Safonovdv91/MG-Lap-Race-Timer/src/modules/web_handlers.cpp

/** 
 * Обработчики веб-запросов.
 */
#include <ArduinoJson.h>
#include <FS.h>
#include <SPIFFS.h>

#include "modules/web_handlers.h"
#include "utils/config.h"
#include "core/measurement_core.h"
#include "modules/web_content.h"
#include "drivers/battery/battery.h"

#ifdef RECEIVER_MODE
#include "modules/transmitter_data.h"  // ← теперь всё живёт здесь
#endif

WebServer server(80);

// Внешние переменные (определены в других файлах)
extern Mode currentMode;

// Переменные для хранения данных излучателя (только для режима приемника)
#ifdef RECEIVER_MODE

#endif

// ============================================================================
// * Все данные обновляются через WebSocket (JavaScript)
// ============================================================================

void sendHtmlFile(const char* path) {
  if (SPIFFS.exists(path)) {
    File file = SPIFFS.open(path, "r");
    if (file) {
      server.streamFile(file, "text/html");
      file.close();
    } else {
      server.send(500, "text/plain", "File open failed");
    }
  } else {
    server.send(404, "text/plain", "File not found");
  }
}

// ============================================================================
// Web Handlers
// ============================================================================

void handleRoot() {
  sendHtmlFile("/index.html");
}

void handleReset() {
  resetMeasurementsCore();
  server.send(200, "text/plain", "OK");
}

void handleMode() {
  String modeParam = server.arg("m");
  if(modeParam != "") {
    int mode = modeParam.toInt();
    if(mode >= 0 && mode <= 2) {
      currentMode = (Mode)mode;
    }
  }
  server.send(200, "text/plain", String(currentMode));
}

void handleCSS() {
  if(SPIFFS.exists("/style.css")) {
    File file = SPIFFS.open("/style.css", "r");
    if(file) {
      server.streamFile(file, "text/css");
      file.close();
    } else {
      server.send(404, "text/plain", "File not found");
    }
  } else {
    server.send(200, "text/css", "");
  }
}

void handleJS() {
  if(SPIFFS.exists("/script.js")) {
    File file = SPIFFS.open("/script.js", "r");
    if(file) {
      server.streamFile(file, "application/javascript");
      file.close();
    } else {
      server.send(404, "text/plain", "File not found");
    }
  } else {
    server.send(200, "application/javascript", "");
  }
}

void handleWiFiSettings() {
  sendHtmlFile("/wifi_settings.html");
}

/**
 * API для получения текущих Wi-Fi настроек
 */
void handleGetWifiSettings() {
  StaticJsonDocument<256> doc;
  doc["ssid"] = ssid;
  doc["password"] = password;
  
  String json;
  serializeJson(doc, json);
  server.sendHeader("Content-Type", "application/json; charset=utf-8");
  server.send(200, "application/json", json);
}

/**
 * API для обновления пароля Wi-Fi
 * Проверяет старый пароль, устанавливает новый
 */
void handleUpdateWifiPassword() {
  if (server.method() != HTTP_POST) {
    server.send(405, "text/plain", "Method Not Allowed");
    return;
  }
  
  // Парсинг JSON тела запроса
  StaticJsonDocument<512> doc;
  DeserializationError error = deserializeJson(doc, server.arg("plain"));
  
  if (error) {
    String json = "{\"success\":false,\"message\":\"Invalid JSON\"}";
    server.sendHeader("Content-Type", "application/json; charset=utf-8");
    server.send(400, "application/json", json);
    return;
  }
  
  const char* oldPassword = doc["oldPassword"];
  const char* newPassword = doc["newPassword"];
  
  // Валидация входных данных
  if (!oldPassword || !newPassword) {
    String json = "{\"success\":false,\"message\":\"Missing password fields\"}";
    server.sendHeader("Content-Type", "application/json; charset=utf-8");
    server.send(400, "application/json", json);
    return;
  }
  
  // Проверка старого пароля
  if (strcmp(oldPassword, password) != 0) {
    String json = "{\"success\":false,\"message\":\"Неверный текущий пароль\"}";
    server.sendHeader("Content-Type", "application/json; charset=utf-8");
    server.send(403, "application/json", json);
    return;
  }
  
  // Валидация нового пароля
  size_t newPassLen = strlen(newPassword);
  if (newPassLen < 8 || newPassLen > 64) {
    String json = "{\"success\":false,\"message\":\"Пароль должен быть от 8 до 64 символов\"}";
    server.sendHeader("Content-Type", "application/json; charset=utf-8");
    server.send(400, "application/json", json);
    return;
  }
  
  // Сохранение нового пароля
  strncpy(password, newPassword, sizeof(password) - 1);
  password[sizeof(password) - 1] = '\0';
  saveWiFiSettings();
  
  // Логирование (для отладки)
  Serial.printf("[WiFi] Пароль изменён. Новый: %s\n", password);
  
  // Успешный ответ
  String json = "{\"success\":true,\"message\":\"Пароль изменён\"}";
  server.sendHeader("Content-Type", "application/json; charset=utf-8");
  server.send(200, "application/json", json);
}

void handleUpdateWiFi() {
  String newSSID = server.arg("ssid");
  String newPassword = server.arg("password");

  if(newSSID.length() > 0 && newSSID.length() < 32) {
    strncpy(ssid, newSSID.c_str(), sizeof(ssid) - 1);
    ssid[sizeof(ssid) - 1] = '\0';
  }

  if(newPassword.length() < 64) {
    strncpy(password, newPassword.c_str(), sizeof(password) - 1);
    password[sizeof(password) - 1] = '\0';
  }

  saveWiFiSettings();

  server.sendHeader("Location", "/");
  server.send(303);
}
